Mark-MDO47/Skull-Project/resources/images/CB_Closed_3d_OprSide.jpg

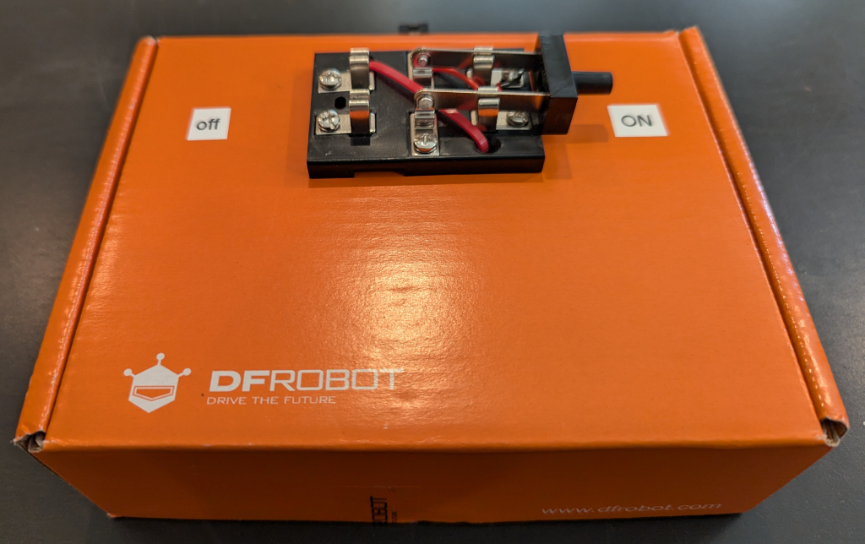
resources/images/CB_Closed_3d_OprSide.jpg
