Mark-MDO47/Skull-Project/resources/images/CB_Closed_top.jpg

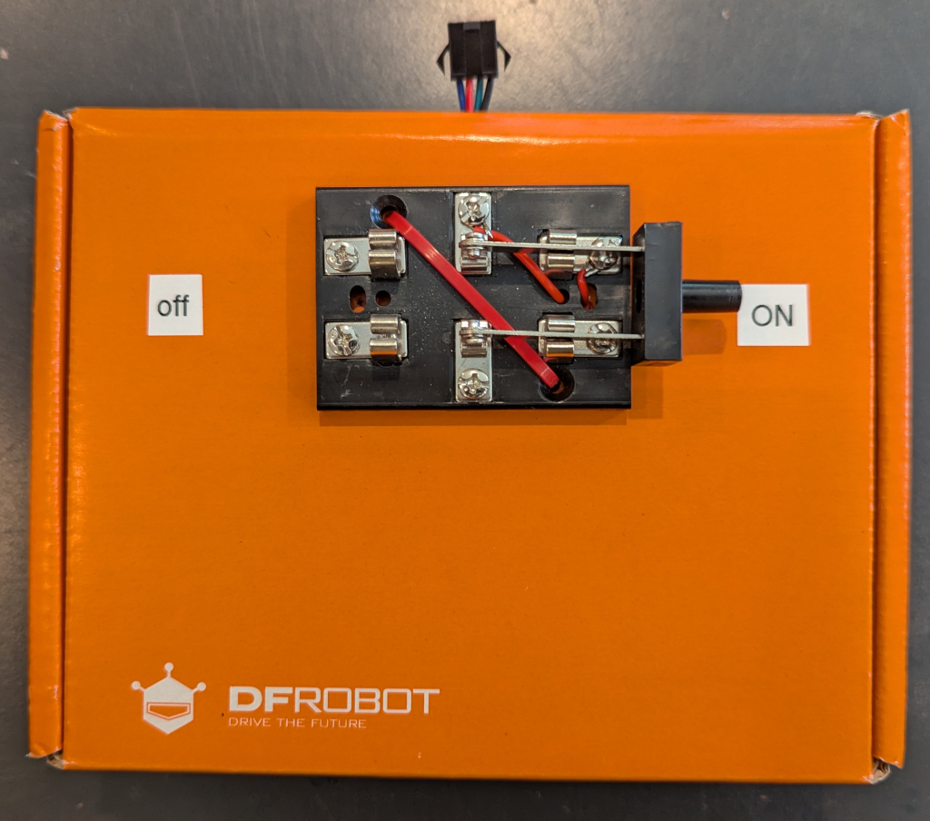
resources/images/CB_Closed_top.jpg
