Mark-MDO47/Skull-Project/resources/images/KnifeSwitch_02.jpg

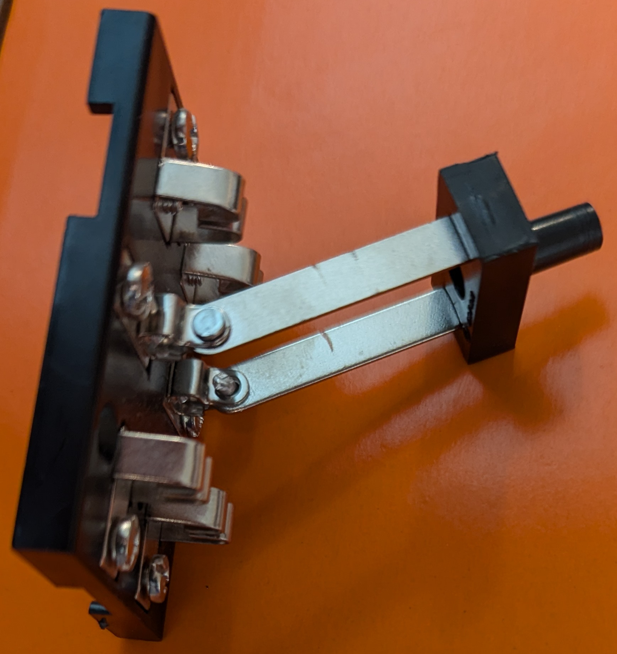
resources/images/KnifeSwitch_02.jpg
