Mark-MDO47/Skull-Project/resources/images/PushButtonSwitch12mm_dimensions.png

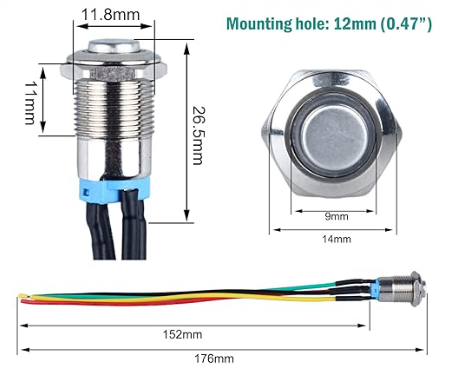
resources/images/PushButtonSwitch12mm_dimensions.png
