Mark-MDO47/Skull-Project/resources/images/PushButtonSwitch12mm_LifeRating.png

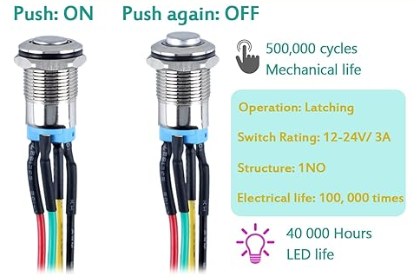
resources/images/PushButtonSwitch12mm_LifeRating.png
