Mark-MDO47/Skull-Project/resources/images/RS_FlipFlop_StateDiagram.png

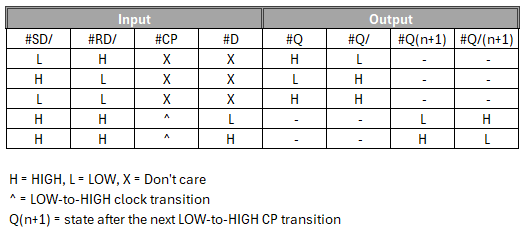
resources/images/RS_FlipFlop_StateDiagram.png
