Mark-MDO47/Skull-Project/resources/images/skull_prjct_before_cutting.jpg

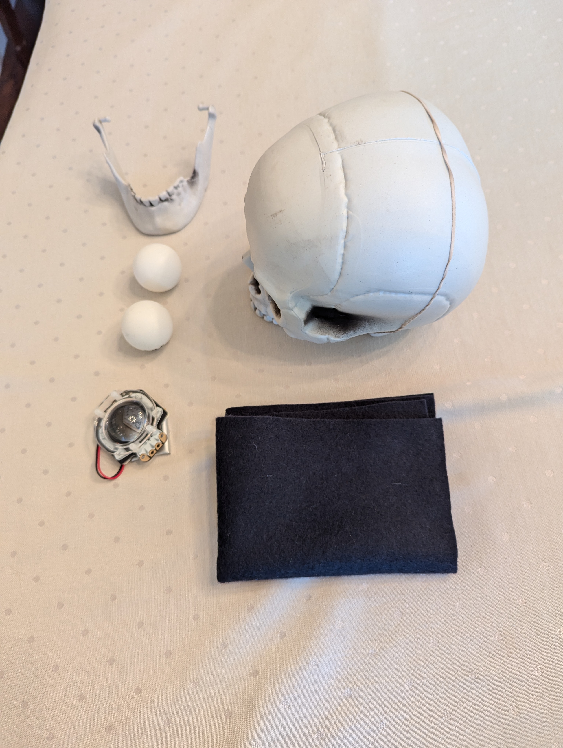
resources/images/skull_prjct_before_cutting.jpg
