Mark-MDO47/Skull-Project/resources/images/skull_prjct_RCWL-0516_and_radome.jpg

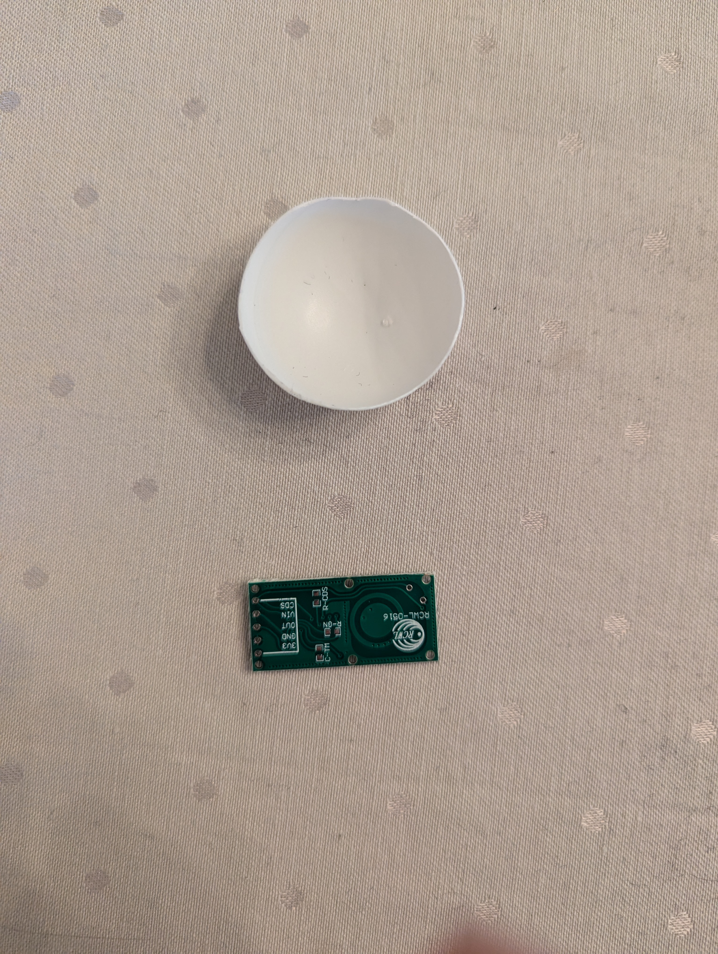
resources/images/skull_prjct_RCWL-0516_and_radome.jpg
