Mark-MDO47/Skull-Project/resources/images/skull_prjct_sideview.jpg

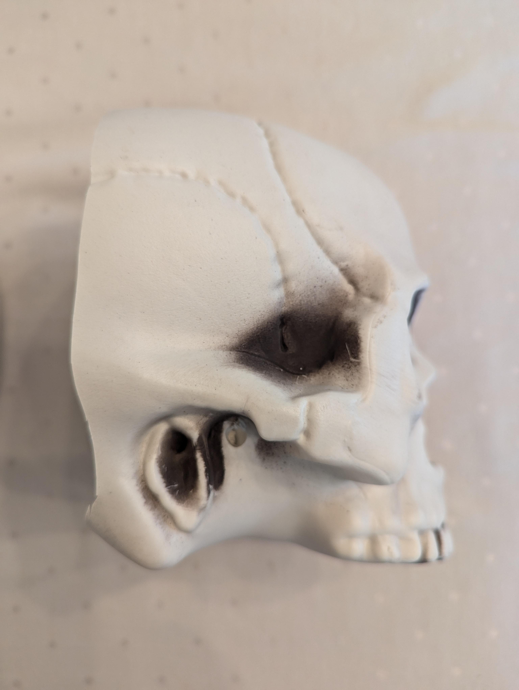
resources/images/skull_prjct_sideview.jpg
