Mark-MDO47/Skull-Project/resources/images/skull_prjct_RCWL-0516_test_trace_5secperdiv.jpg

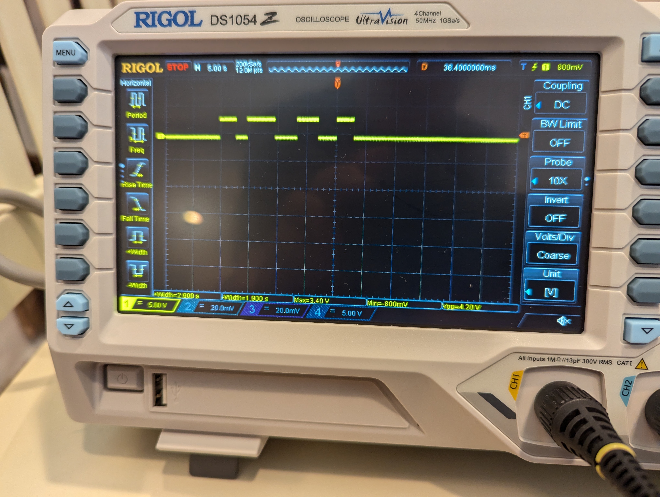
resources/images/skull_prjct_RCWL-0516_test_trace_5secperdiv.jpg
