Mark-MDO47/Skull-Project/resources/KiCad/Skull-Project_1.0/PersonSensor.kicad_sch

## KiCad design resources/KiCad/Skull-Project_1.0/PersonSensor.kicad_sch (2025-08-10, an earlier design)

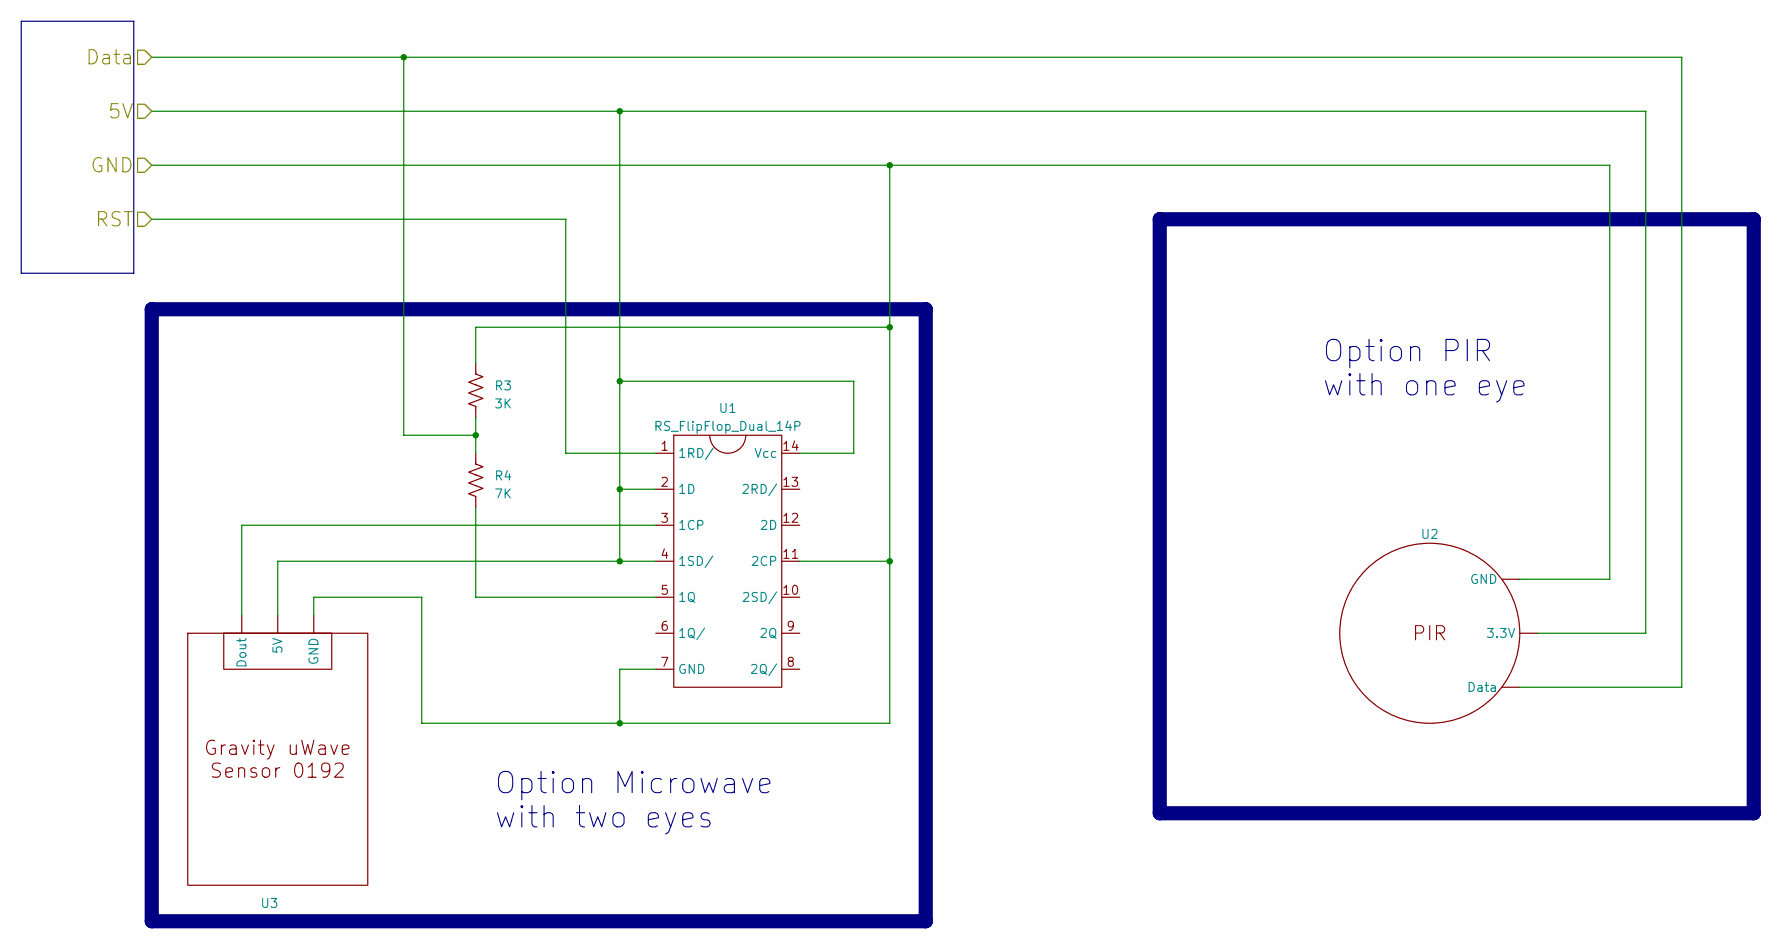
[picture p45: schematic PersonSensor.kicad_sch]

Parts:
R3: 3K
R4: 7K
U1: RS_FlipFlop_Dual_14P
U2, U3: (no value)

Connections:
5V: U1.2 (1D), U1.4 (1SD/), U1.14 (Vcc), U2., U3.
Data: R3.2, R4.1, U2.
GND: R3.1, U1.7 (GND), U1.11 (2CP), U2., U3.
unnamed: R4.2, U1.5 (1Q)
unnamed: U1.3 (1CP), U3.
RST: U1.1 (1RD/)

Notes on the sheet:
Option Microwave with two eyes
Option PIR with one eye
