Mark-MDO47/Skull-Project/resources/KiCad/Skull-Project_1.0/Skull-Project_1.0.kicad_sch

## KiCad design resources/KiCad/Skull-Project_1.0/Skull-Project_1.0.kicad_sch (2025-08-10, an earlier design)

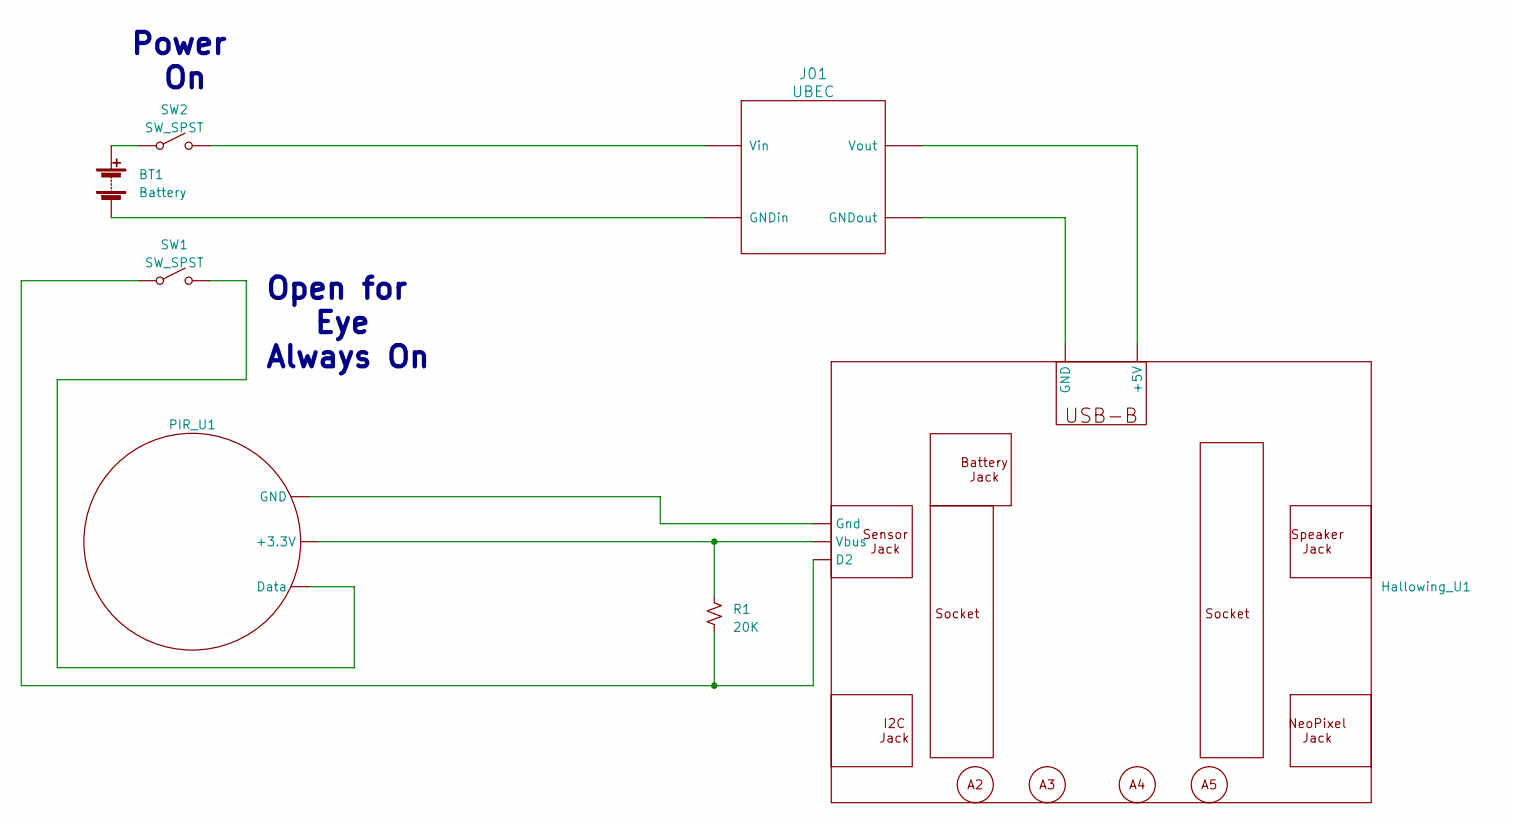
[picture p46: schematic Skull-Project_1.0.kicad_sch]

Parts:
BT1: Battery
Hallowing_U1: (no value)
J01: UBEC
PIR_U1: (no value)
R1: 20K
SW1, SW2: SW_SPST

Connections:
unnamed: BT1.1 (+), SW2.~
unnamed: BT1.2 (-), J01.~
unnamed: Hallowing_U1., J01.~, PIR_U1., R1.1, R1.2, SW1.~
unnamed: J01.~, SW2.~
unnamed: PIR_U1., SW1.~

Notes on the sheet:
Power On
Open for Eye Always On
